depletionmode/cupc8/doc/dev-environment.md

# Development environment

What the test suite (`make test`, `test/run.py`) needs, and how to get it on a
stock Ubuntu 24.04 machine such as a cloud container. `tools/setup_ubuntu.sh`
does everything except KiCad.

| Tool | Used by | Where it comes from |
|---|---|---|
| OSS CAD Suite: GHDL, Yosys + ghdl plugin, Verilator, SBY, bitwuzla, nextpnr | HDL, formal, synthesis, the whole-machine emulator's main board | the YosysHQ release tarball in `/opt/oss-cad-suite`. Ubuntu's packages are too old: Yosys 0.33's smtbmc fails BUS-004's induction step and passes bitwuzla 0.1's command line. |
| Nim + sdl2 | `tools/sim.nim` and its tests | apt `nim`; the `sdl2` wrapper from git (`~/.config/nim/nim.cfg` points at it) |
| arm-none-eabi-gcc, pico-sdk, PicoDVI, rp2040js | the RP2040 card firmware and its emulated tests | apt; `tools/fetch_sdks.sh` |
| ESP-IDF v5.5.5, Espressif QEMU | the Wi-Fi firmware, WIFI-003, E2E-003 | `tools/fetch_sdks.sh`. If dl.espressif.com is unreachable, `tools/setup_ubuntu.sh` seeds `tools/devenv/espidf.constraints.v5.5.txt` (a hand-written stand-in with the IDF 5.x major versions, not Espressif's file) and sets `IDF_PIP_WHEELS_URL=` so pip uses PyPI only. QEMU and openocd need `libslirp0` and `libusb-1.0-0`. |
| ngspice, TI PSpice models | POW-*, THM-001 | apt; the TI models are fetched from www.ti.com by `hw/power/models/fetch.py` (pinned by SHA-256; not redistributable) |
| NumPy, Matplotlib | WC-005 GND fill and via raster model | apt `python3-numpy`, `python3-matplotlib` |
| KiCad 10, Freerouting | the board tests (BRD-001, WIFI-004, E2E-006, the board rows) | below |

**Emulator and simulator** (David, 2026-09-25):

- **The emulator** is the native whole-machine emulator in `emu/machine`
  (`CUPC8_EMU=native`, built by `tools/emu_machine_build.sh`; see its
  README). It runs the chipset RTL (Verilated) and every card's real
  firmware, and must be **cycle perfect**; the end-to-end tests
  (`test/emu/test_e2e.mjs`) run on it. `test/emu/machine.mjs` (rp2040js) is
  the legacy JS emulator, kept but no longer updated. Watch it in a browser
  with `tools/machine_view.mjs --native`.
- **The simulator** (`tools/sim`, from `tools/sim.nim`) is the interactive
  way to run real CUPC/8 software locally and build programs: the CPU in
  Nim and the cards' firmware cores compiled in (`tools/simcards.nim`). It
  is not cycle exact, but it must always run the current kernel, ROM,
  memory map and card commands.

  Build it with `cd tools && nim c -d:release sim.nim`; `kernel/simulate.sh`
  assembles the kernel and runs it. It simulates the Milestone 1 machine:
  reset runs the boot ROM, which loads the kernel from the ROM image, and
  the slot cards are chosen with `--slots LIST` (default `hdmi,io`):

  ```
  tools/sim --slots hdmi,io,storage,wifi --sd card.img     # the kernel from kernel/
  kernel/simulate.sh --slots eink,io                       # the 5.83" e-ink card
  ```

  Card kinds are the emulator's: `hdmi`, `eink`, `eink750`, `io`,
  `storage`, `wifi` (and `empty`). `--sd IMAGE` is the storage card's SD
  card, a FAT image; a missing file is made as a blank 32 MB FAT16 volume
  (`mkfs.fat`), and a PC reads it afterwards (`tools/fatcheck.py`,
  `mtools`, a loop mount). The Wi-Fi card uses the **host's own sockets**:
  `net join` joins any SSID, and the machine reaches the real network and
  localhost directly (no QEMU, no 10.0.2.x addresses). The window shows
  the graphics card's picture (an e-ink card's glass, which changes only
  when a refresh completes); keys go to the IO card, the arrows, Home, End,
  PgUp, PgDn, Insert, Delete and F1-F12 by their USB HID usages, so the
  kernel gets the IO card's own codes for them ($80-$88, $7f, $91-$9c). `--rom:FILE` boots a
  given ROM image, a `kernel.o` argument is put in one with the boot ROM,
  and `--legacy` keeps the old I/O model (ILI9340, SD on SPI 1). For
  scripts, `--headless --type:"10 print 1\nrun\n" --dump-text:-` types
  the text (a key each time the CPU parks in WAI), runs on for `--settle`
  guest ms once idle, and prints the screen (SIM-010, `test/sim/test_cli.py`);
  in the text `{UP}` `{DOWN}` `{LEFT}` `{RIGHT}` `{HOME}` `{END}` `{PGUP}`
  `{PGDN}` `{INS}` `{DEL}` `{F1}`..`{F12}` or `\xHH` press those keys (SIM-014).
  `--run:PROG` runs a program for $7000 (a `.prg` from `tools/mkprg.py`, or
  the bare binary) once the kernel is at its prompt, as `cupc8.py run` does
  on the machine (SIM-012): `python3 tools/mkprg.py examples/hello/hello.s -o
  hello.prg`, then `tools/sim --run:hello.prg`.
  Guest time is the CPU's clocks, counted as `cpu.vhd` and the chipset spend
  them; the chipset's millisecond counter and the cards follow it. The
  window's sim holds it to the host clock (the speed line then shows 12 MHz
  of CUPC/8 clock), so a program's seconds are wall-clock seconds;
  `--headless` runs as fast as it can.
  `tools/sim --help` lists the rest.

**The USB console** (`doc/proposals/usb-console.md`): the kernel's terminal
on a PC's terminal, both ways.

- **Real hardware:** the system card is two USB serial ports;
  `tools/cupc8.py console` opens the second (interface 2, usually
  `/dev/ttyACM1`; `$CUPC8_CONSOLE` or an argument names another), raw, and
  `Ctrl-]` quits. Any terminal program works as well (`picocom
  /dev/ttyACM1`). Piped, `cupc8.py console < prog.bas` types a program in
  and quits once the machine has been quiet for `--idle` seconds.
- **Emulator:** `node tools/machine_view.mjs --native --console` fits the
  system card and shows the console under the screen, with a box to type or
  paste into; `--console-port 8641` instead serves it on TCP for
  `cupc8.py console tcp:127.0.0.1:8641`. In a script,
  `Machine.create({ sysctl: true })` then `m.console.open()`,
  `m.console.write('run\r')`, `m.console.read()` (`test/emu/machinenative.mjs`).
- **Simulator:** `tools/sim --console` puts the console on the terminal the
  sim runs in: stdout the kernel's output, stdin (raw) typed into the
  machine, `Ctrl-]` quits, the sim's own messages on stderr. With a pipe:
  `tools/sim --headless --console < prog.txt`.

## KiCad 10

The board scripts write KiCad 8 files, which Ubuntu's KiCad 7 cannot read.
Without a KiCad 10 package, the official `kicad/kicad:10.0.6-amd64-full`
container image (from any registry mirror, e.g. mirror.gcr.io) can be
unpacked into `/opt/kicad10` and run as a chroot with
`tools/devenv/kicad10-run`, which bind-mounts `/home`, `/tmp` and the proxy's
CA bundle so paths are the same inside and out:

```
CUPC8_OFFLINE=1 /opt/kicad10-run python3 hw/boards/wifi.py
CUPC8_OFFLINE=1 /opt/kicad10-run python3 test/run.py BRD-001
```

Inside the chroot, add numpy (for `hw/tools/logo.py`) and KiCad's default
global library tables in `/root/.config/kicad/10.0/`. Freerouting 2.4 (a jar
from its GitHub releases) needs Java 25, so it runs on a bundled Temurin JRE
under `/opt/freerouting`. `CUPC8_OFFLINE=1` skips the JLC stock check when
jlcpcb.com is unreachable. Without `KAPLAN_LOGO` (the logo's SVG, not in the
repository), the committed logo footprint is used.

## Hosts

GitHub (git and release assets), PyPI, the Ubuntu archive; www.ti.com for the
power models; jlcpcb.com for stock checks; dl.espressif.com is optional.
